RaphWeyman/CANPower/Software/CANPower.X/configuration_bits.c

// PIC24HJ128GP504 Configuration Bit Settings

// 'C' source line config statements

// FBS
#pragma config BWRP = WRPROTECT_OFF     // Boot Segment Write Protect (Boot Segment may be written)
#pragma config BSS = NO_FLASH           // Boot Segment Program Flash Code Protection (No Boot program Flash segment)
#pragma config RBS = NO_RAM             // Boot Segment RAM Protection (No Boot RAM)

// FSS
#pragma config SWRP = WRPROTECT_OFF     // Secure Segment Program Write Protect (Secure segment may be written)
#pragma config SSS = NO_FLASH           // Secure Segment Program Flash Code Protection (No Secure Segment)
#pragma config RSS = NO_RAM             // Secure Segment Data RAM Protection (No Secure RAM)

// FGS
#pragma config GWRP = OFF               // General Code Segment Write Protect (User program memory is not write-protected)
#pragma config GSS = OFF                // General Segment Code Protection (User program memory is not code-protected)

// FOSCSEL
#pragma config FNOSC = FRC              // Oscillator Mode (Internal Fast RC (FRC))
#pragma config IESO = ON                // Internal External Switch Over Mode (Start-up device with FRC, then automatically switch to user-selected oscillator source when ready)

// FOSC
#pragma config POSCMD = XT              // Primary Oscillator Source (XT Oscillator Mode)
#pragma config OSCIOFNC = OFF           // OSC2 Pin Function (OSC2 pin has clock out function)
#pragma config IOL1WAY = OFF            // Peripheral Pin Select Configuration (Allow Multiple Re-configurations)
#pragma config FCKSM = CSECME           // Clock Switching and Monitor (Both Clock Switching and Fail-Safe Clock Monitor are enabled)

// FWDT
#pragma config WDTPOST = PS64           // Watchdog Timer Postscaler (1:64)
#pragma config WDTPRE = PR32            // WDT Prescaler (1:32)
#pragma config WINDIS = OFF             // Watchdog Timer Window (Watchdog Timer in Non-Window mode)
#pragma config FWDTEN = ON              // Watchdog Timer Enable (Watchdog timer always enabled)

// FPOR
#pragma config FPWRT = PWR128           // POR Timer Value (128ms)
#pragma config ALTI2C = OFF             // Alternate I2C  pins (I2C mapped to SDA1/SCL1 pins)

// FICD
#pragma config ICS = PGD3               // Comm Channel Select (Communicate on PGC3/EMUC3 and PGD3/EMUD3)
#pragma config JTAGEN = OFF             // JTAG Port Enable (JTAG is Disabled)

// #pragma config statements should precede project file includes.
// Use project enums instead of #define for ON and OFF.
#include <xc.h>
