RaphWeyman/CANPower/Software/CANPower.X/interrupts.h

/* 
 * File:   interrupts.h
 * Author: Raph Weyman
 *
 * Created on 07 November 2017, 10:03
 * 
 * For interrupt priority definitions
 */

#ifndef INTERRUPTS_H
#define	INTERRUPTS_H


#define TIMER_INTERRUPT_PRIORITY 2
#define SPI_INTERRUPT_PRIORITY 3
#define CAN_INTERRUPT_PRIORITY 4



#ifdef	__cplusplus
extern "C" {
#endif




#ifdef	__cplusplus
}
#endif

#endif	/* INTERRUPTS_H */
